ClusterM/famicom-dumper-writer/FamicomDumper/Core/Inc/led.h

#ifndef _LED_H_
#define _LED_H_

void set_led_color(uint8_t r, uint8_t g, uint8_t b);
void led_off();
void led_white();
void led_green();
void led_red();;
void led_yellow();
void led_blue();
void led_magenta();
void led_cyan();
void led_idle();

#endif
